bababooex/DMP-rizeni-prijimace/Program/inc/disp_perks.h

#ifndef DISP_PERKS_H
#define DISP_PERKS_H
#include "stm8_hd44780.h"
//Before using this library, call bigfont_init() first!
/**
 * @brief functions regarding this library
 * - Display perks for other things regarding lower part of lcd
 */
void perks_show(void);
#endif // DISP_PERKS_H
