bababooex/DMP-rizeni-prijimace/Program/inc/guide.h

#ifndef GUIDE_H
#define GUIDE_H

#include "stm8_hd44780.h"
#include "stm8s_delay.h"
/**
 * @brief User guide when turning on the device for first time
 * - display brief info before start
 */
void display_guide(void);

#endif // AUTOSET_H
